claudinoac/metereolog/backend/sensor/api/urls.py

from sensor.api import views
from django.urls import path


urlpatterns = [
    path("<uuid:sensor_uid>/chart", views.SensorChartView.as_view()),
    path("<uuid:sensor_uid>", views.SensorViewSet.as_view({"get": "retrieve", "delete": "delete"})),
]
