claudinoac/metereolog/backend/iam/api/authentication.py

from rest_framework.authentication import SessionAuthentication


class SessionAuthentication(SessionAuthentication):

    def enforce_csrf(self, request):
        return

    def authenticate_header(self, request):
        return 'session'
